electgpl/Utn-labMicros-Est/Documentación/Imagenes/apara-elec.jpg

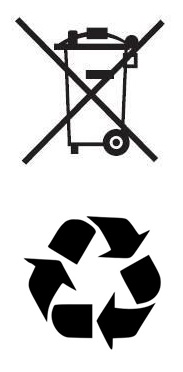
Documentación/Imagenes/apara-elec.jpg
