electgpl/Utn-labMicros-Est/Documentación/Imagenes/Diagrama C8051F832.png

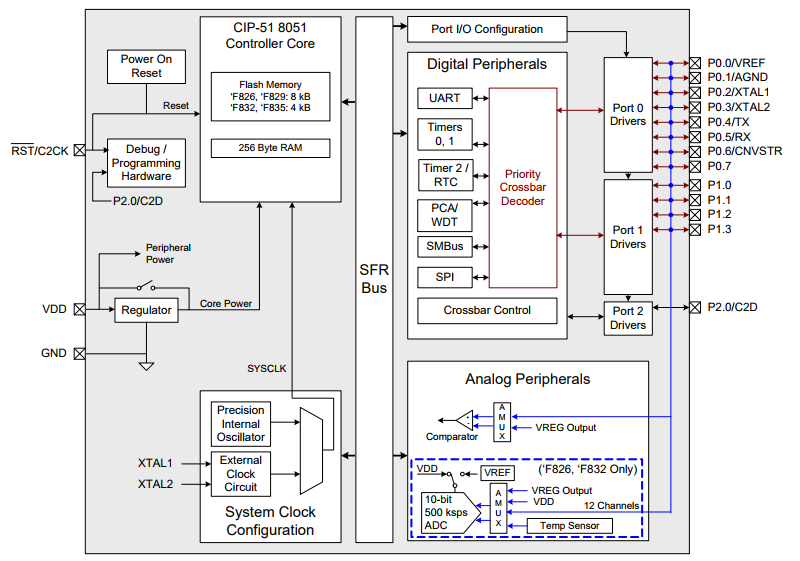
Documentación/Imagenes/Diagrama C8051F832.png
