electgpl/Utn-labMicros-Est/Documentación/Imagenes/Estacion Meteorologica.png

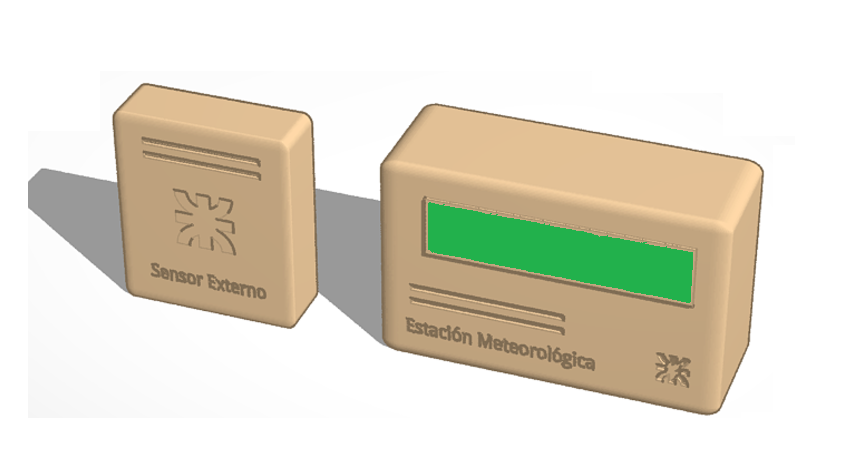
Documentación/Imagenes/Estacion Meteorologica.png
