electgpl/Utn-labMicros-Est/Documentación/Imagenes/lcd.jpg

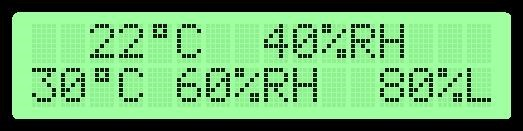
Documentación/Imagenes/lcd.jpg
