electgpl/Utn-labMicros-Est/Documentación/Imagenes/plano ejemplo display.png

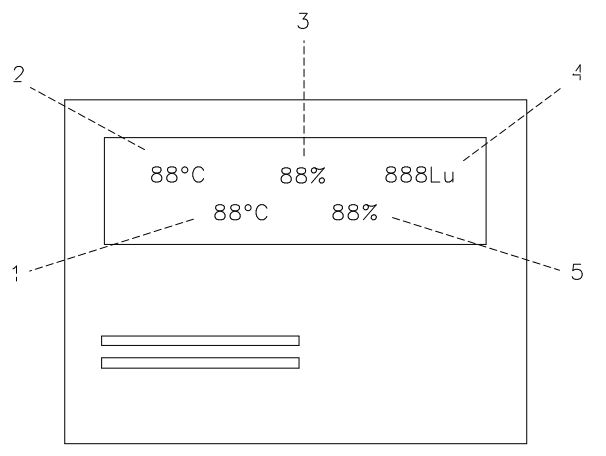
Documentación/Imagenes/plano ejemplo display.png
