electgpl/Utn-labMicros-Est/Documentación/Imagenes/plano sensor interno.png

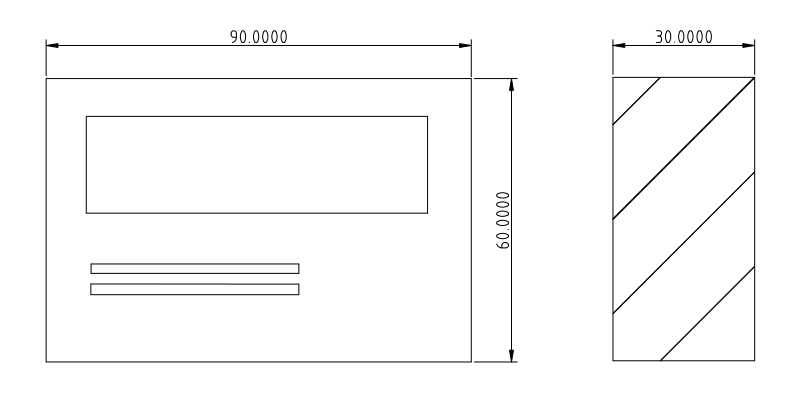
Documentación/Imagenes/plano sensor interno.png
