electgpl/Utn-labMicros-Est/Documentación/Imagenes/Sensor Externo Dimensiones.png

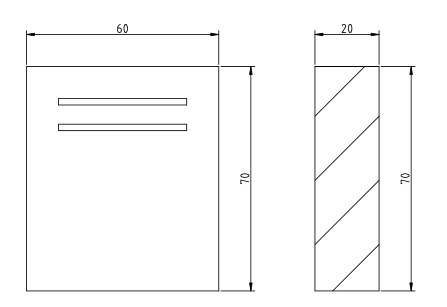
Documentación/Imagenes/Sensor Externo Dimensiones.png
