electgpl/Utn-labMicros-Est/Hardware Estación Interna y Externa/UTN-ESEXT01/UTN-ESEXT01-TOP.png

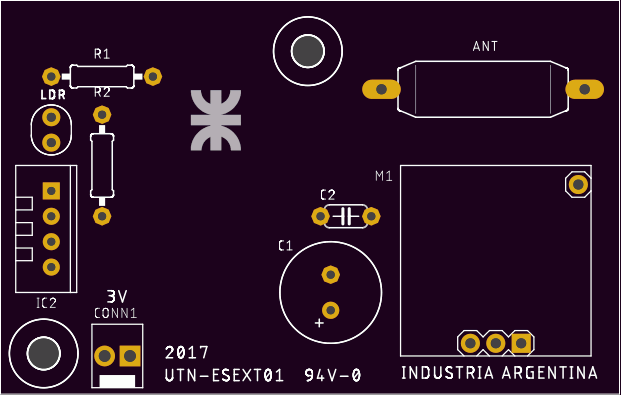
Hardware Estación Interna y Externa/UTN-ESEXT01/UTN-ESEXT01-TOP.png
