electgpl/Utn-labMicros-Est/Hardware Estación Interna y Externa/UTN-ESINT01/UTN-ESINT01-BOTTOM.png

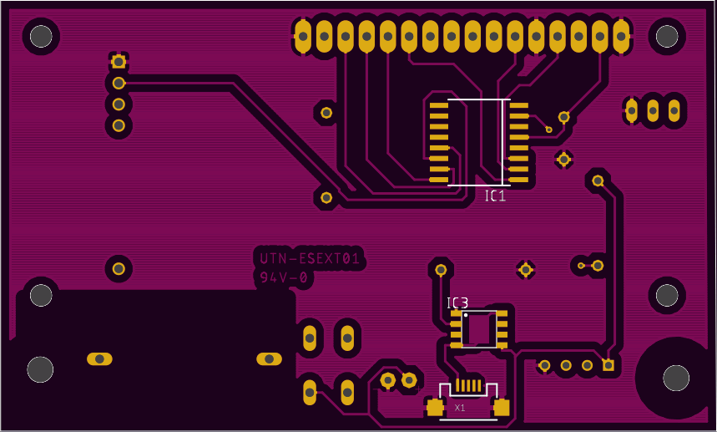
Hardware Estación Interna y Externa/UTN-ESINT01/UTN-ESINT01-BOTTOM.png
